Kostas-F/pwrtch-slider-mod/images/01.jpg

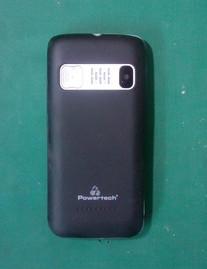
images/01.jpg
